NDMDevel/TD3_Filter/INIT.h

/* 
 * File:   INIT.h
 * Author: Damian
 *
 * Created on 5 de junio de 2018, 16:02
 */

#ifndef INIT_H
#define	INIT_H

#ifdef	__cplusplus
extern "C" {
#endif

#define INICIALIZACION =\
{\
    0,\
    1,\
    2,\
    3,\
    4\
}


#ifdef	__cplusplus
}
#endif

#endif	/* INIT_H */
