NDMDevel/TD3_Filter/TD3_InitData.h

#ifndef TD3_INITDATA_H
#define TD3_INITDATA_H

#define N	128
#define Nminus1	N-1

#define TD3_LOAD_MACRO =\
{\
	0x0000,0x0000,0x0000,0x0000,0x0000,0x0001,\
	0x0003,0x0001,0x0004,0x0000,0xfffb,0x0001,\
	0xfff3,0x0001,0x0000,0x0001,0x001c,0x0000,\
	0x0018,0x0000,0xffe1,0x0000,0xffbd,0x0001,\
	0x0000,0x0001,0x006f,0x0000,0x0057,0x0000,\
	0xff95,0x0000,0xff2a,0x0001,0x0000,0x0001,\
	0x0140,0x0000,0x00f0,0x0000,0xfee1,0x0000,\
	0xfdd1,0x0001,0x0000,0x0001,0x0326,0x0000,\
	0x0259,0x0000,0xfd29,0x0000,0xfa5a,0x0001,\
	0x0000,0x0001,0x0928,0x0000,0x07bf,0x0000,\
	0xf42d,0x0000,0xd957,0x0001,0x4cc8,0x0001,\
	0xd97f,0x0000,0xf445,0x0000,0x07a7,0x0000,\
	0x0902,0x0001,0x0000,0x0001,0xfa7d,0x0000,\
	0xfd3d,0x0000,0x0245,0x0000,0x0309,0x0001,\
	0x0000,0x0001,0xfdea,0x0000,0xfeef,0x0000,\
	0x00e2,0x0000,0x012d,0x0001,0x0000,0x0001,\
	0xff39,0x0000,0xff9d,0x0000,0x0050,0x0000,\
	0x0065,0x0001,0x0000,0x0001,0xffc4,0x0000,\
	0xffe4,0x0000,0x0015,0x0000,0x0019,0x0001,\
	0x0000,0x0001,0xfff5,0x0001,0xfffc,0x0000,\
	0x0003,0x0001,0x0002,0x0001,0x0000,0x0000,\
	0x0000,0x0000\
};

#endif
